thomotron/The-Gelsoft-Bomb-Project/Arduino Sketches/module_keypad/randomvals.h

/* generated using: http://atoomnet.net/?p=462 */

#ifndef RANDOMVALS_H_
#define RANDOMVALS_H_

//100 guaranteed random numbers
const uint8_t random0[] PROGMEM = {
  0xC6, 0xF2, 0xD5, 0x3B, 0xFD, 0x53, 0x2E, 0x6E, 0xF8, 0xBB, 0x4B, 0x47, 0xD5, 0xC9, 0x77, 0xB0, 0xC4, 0xD7, 0xAB, 0x78, 0x62, 0x39, 0xB9, 0x15, 0xE1, 0x77, 0xAD, 0xF6, 0xC7, 0x59, 0x0A, 0x38,
  0x21, 0xD2, 0x84, 0x2D, 0x3D, 0x0B, 0x11, 0xCD, 0x45, 0xC4, 0xA9, 0x8F, 0xE8, 0x5F, 0xE0, 0x7D, 0xE6, 0xC7, 0x16, 0xC0, 0x25, 0x32, 0x38, 0x70, 0x88, 0x1B, 0x3C, 0xC4, 0xD9, 0x3F, 0x03, 0x16,
  0x6B, 0xB6, 0x7B, 0xC9, 0x28, 0x46, 0xCF, 0x39, 0x40, 0x56, 0x2F, 0x13, 0xA6, 0x3E, 0xFD, 0x19, 0xAA, 0x3C, 0xCC, 0x62, 0x79, 0xA1, 0x73, 0x0B, 0xCD, 0xDE, 0xDC, 0x30, 0x1A, 0x3E, 0x4B, 0x69,
  0x95, 0x0F, 0xC9, 0x1D
};

#endif /* RANDOMVALS_H_ */
